ayuusweetfish/BEEPBUG/flowerbed/fw_unit/src/vl53l0x/vl53l0x_i2c_platform.h

/*
 * COPYRIGHT (C) STMicroelectronics 2014. All rights reserved.
 *
 * This software is the confidential and proprietary information of
 * STMicroelectronics ("Confidential Information").  You shall not
 * disclose such Confidential Information and shall use it only in
 * accordance with the terms of the license agreement you entered into
 * with STMicroelectronics
 *
 * Programming Golden Rule: Keep it Simple!
 *
 */

/**
 * @file   VL53L0X_platform.h
 * @brief  Function prototype definitions for Ewok Platform layer.
 *
 */


#ifndef _VL53L0X_I2C_PLATFORM_H_
#define _VL53L0X_I2C_PLATFORM_H_
#endif //_VL53L0X_I2C_PLATFORM_H_
